Tinkerforge/distance-us-v2-bricklet-techniker/Dokumentation/Ausarbeitung Technikerprojekt/0_Titelseite.tex

\begin{center}
\begin{Huge}
\textcolor{blue}{\textbf{Entwicklung und testen eines Ultraschall-Entfernungsmessers als Vorbereitung eines Produktentwurfes}}
\end{Huge}
\rule{\textwidth}{.4pt}
\vspace{1.5cm}
% Weiter in großer Schrift

\huge{\textbf{Projektarbeit}}\\
\begin{Large}
erstellt an der\\
Fachschule für Technik des Carl-Severing-Berufskolleg\\
für Metall- und Elektrotechnik der Stadt Bielefeld\\
\\

Erstellt durch:\\
\vspace{12pt}
Eduard Meiser\\Omar Hachimi \\Stephan Dannat\\FET6A\\
\vspace{12pt}
in Zusammenarbeit mit der Fa. Tinkerforge\\
betreut durch\\
Herrn Simon\\
Bielefeld, \today
\end{Large}
\end{center}
