Tinkerforge/distance-us-v2-bricklet-techniker/Dokumentation/Anhänge/C4016L8A40_Ultraschallsensor.pdf

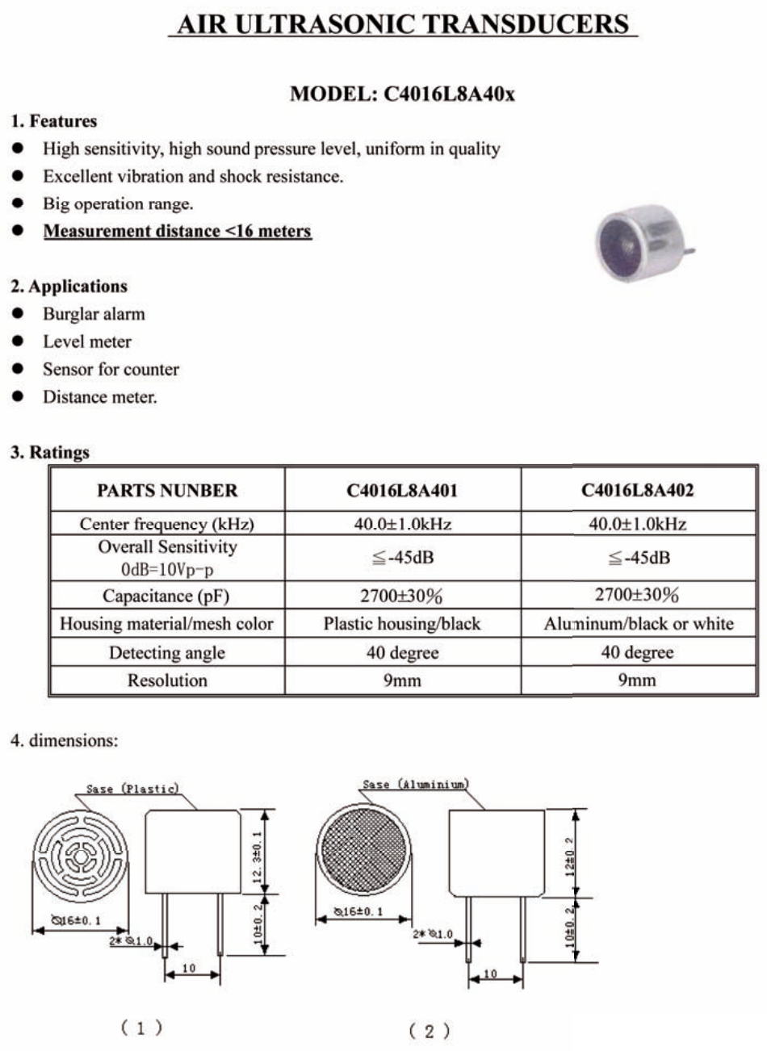
[picture p30: page 1]
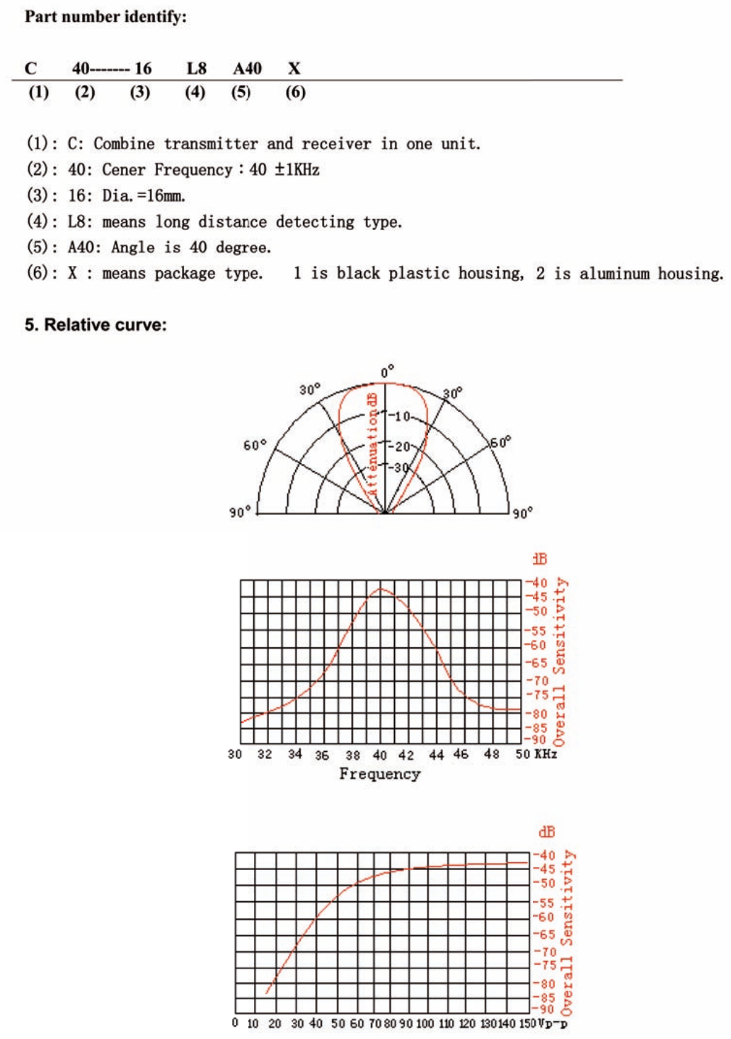
[picture p31: page 2]
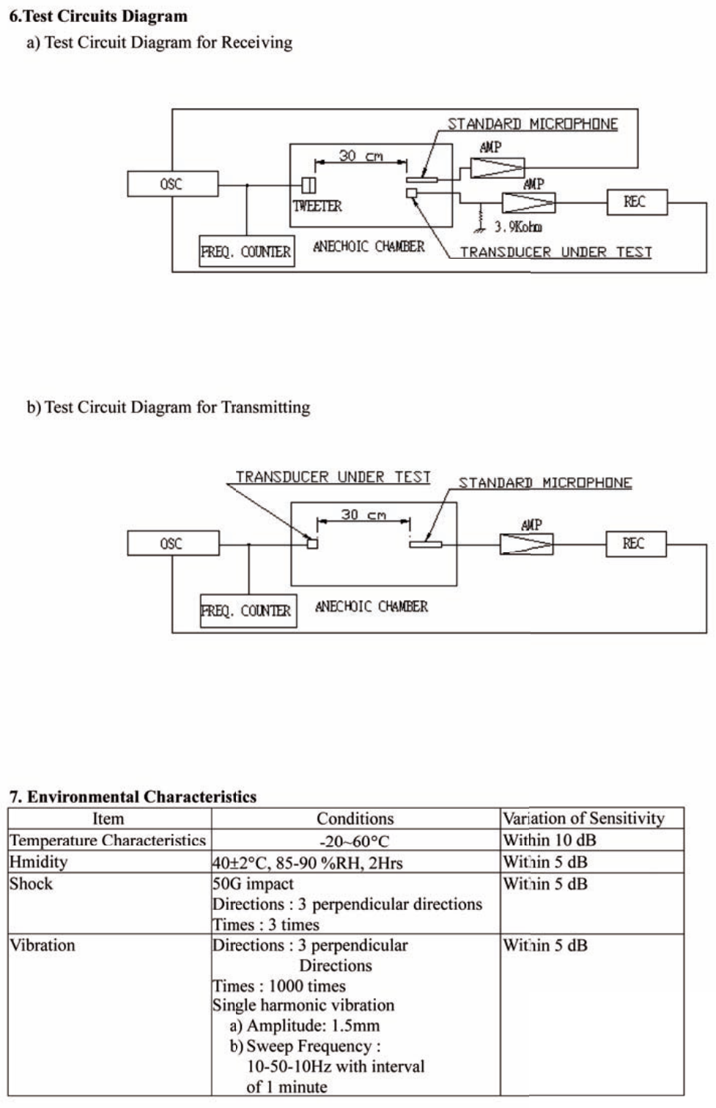
[picture p32: page 3]
