Tinkerforge/distance-us-v2-bricklet-techniker/Dokumentation/Ausarbeitung Technikerprojekt/Abbildungen/A5950/H_Brücke.jpg

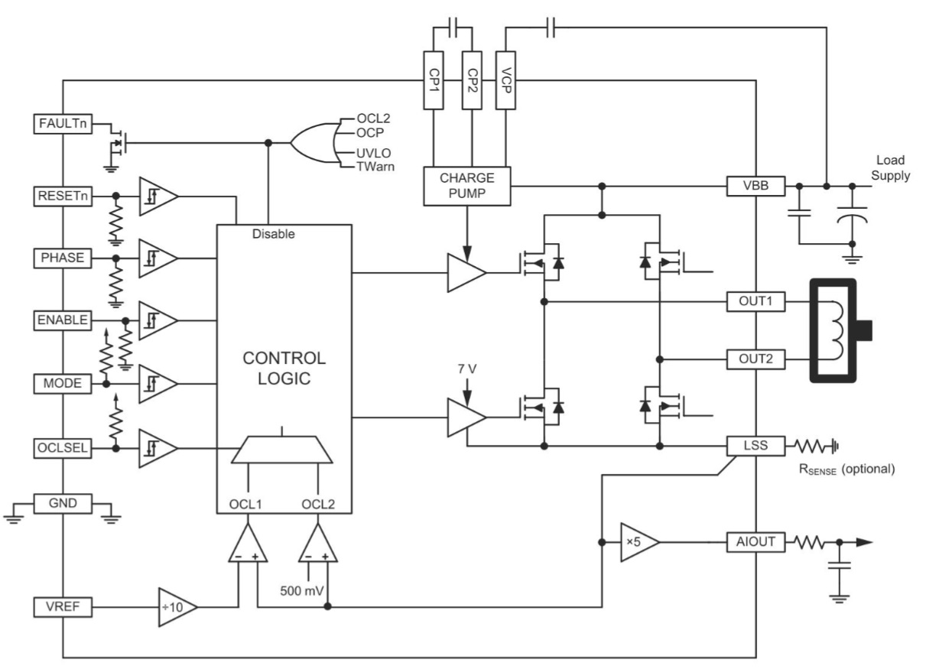
Dokumentation/Ausarbeitung Technikerprojekt/Abbildungen/A5950/H_Brücke.jpg
