Tinkerforge/distance-us-v2-bricklet-techniker/Dokumentation/Ausarbeitung Technikerprojekt/Abbildungen/Empfaenger.png

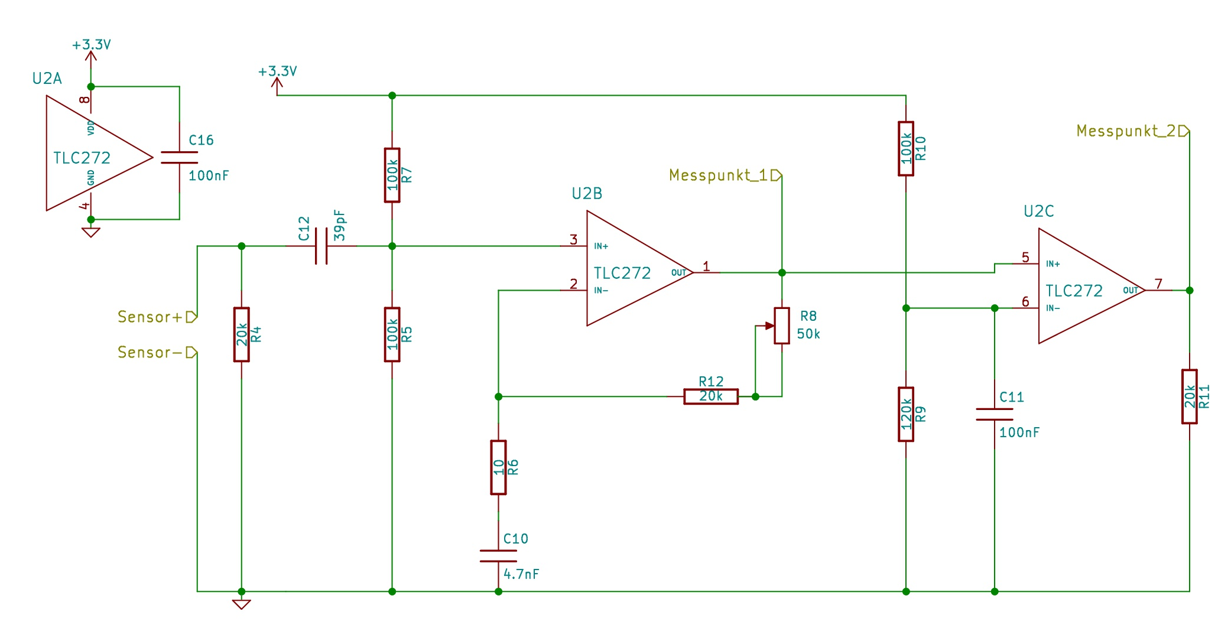
Dokumentation/Ausarbeitung Technikerprojekt/Abbildungen/Empfaenger.png
