Tinkerforge/distance-us-v2-bricklet-techniker/Dokumentation/Ausarbeitung Technikerprojekt/Abbildungen/h-side.jpg

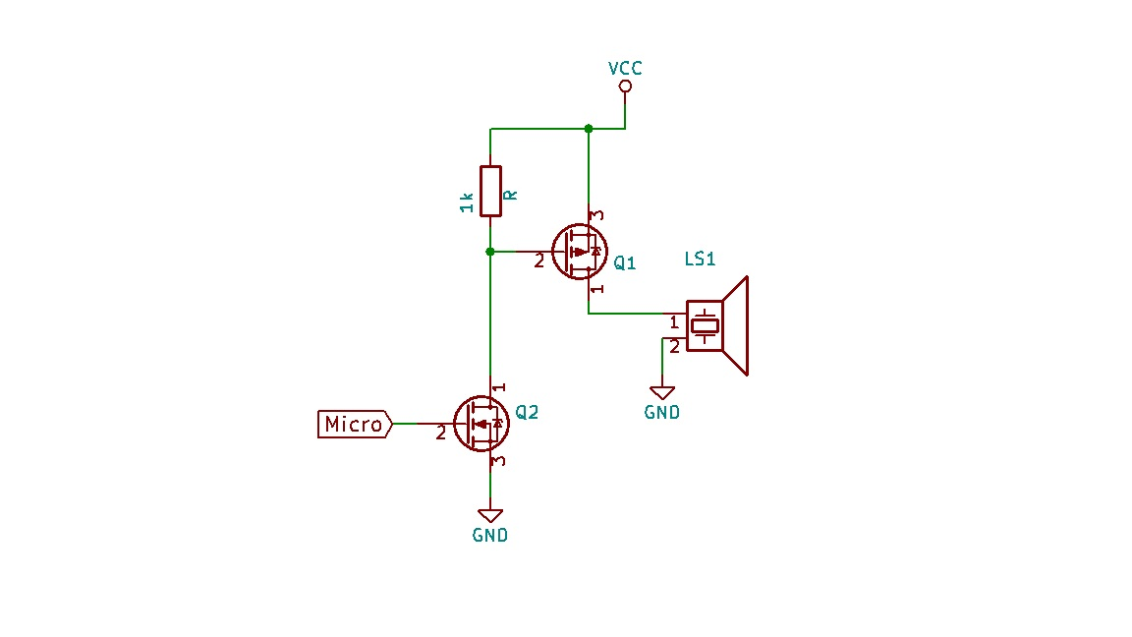
Dokumentation/Ausarbeitung Technikerprojekt/Abbildungen/h-side.jpg
