Tinkerforge/distance-us-v2-bricklet-techniker/Dokumentation/Ausarbeitung Technikerprojekt/Abbildungen/h-side.png

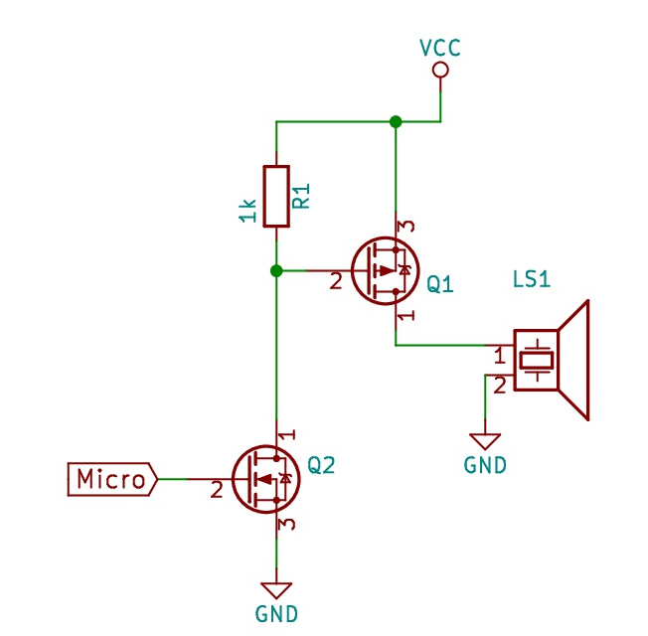
Dokumentation/Ausarbeitung Technikerprojekt/Abbildungen/h-side.png
