Tinkerforge/distance-us-v2-bricklet-techniker/Dokumentation/Ausarbeitung Technikerprojekt/Abbildungen/halbbrucke.png

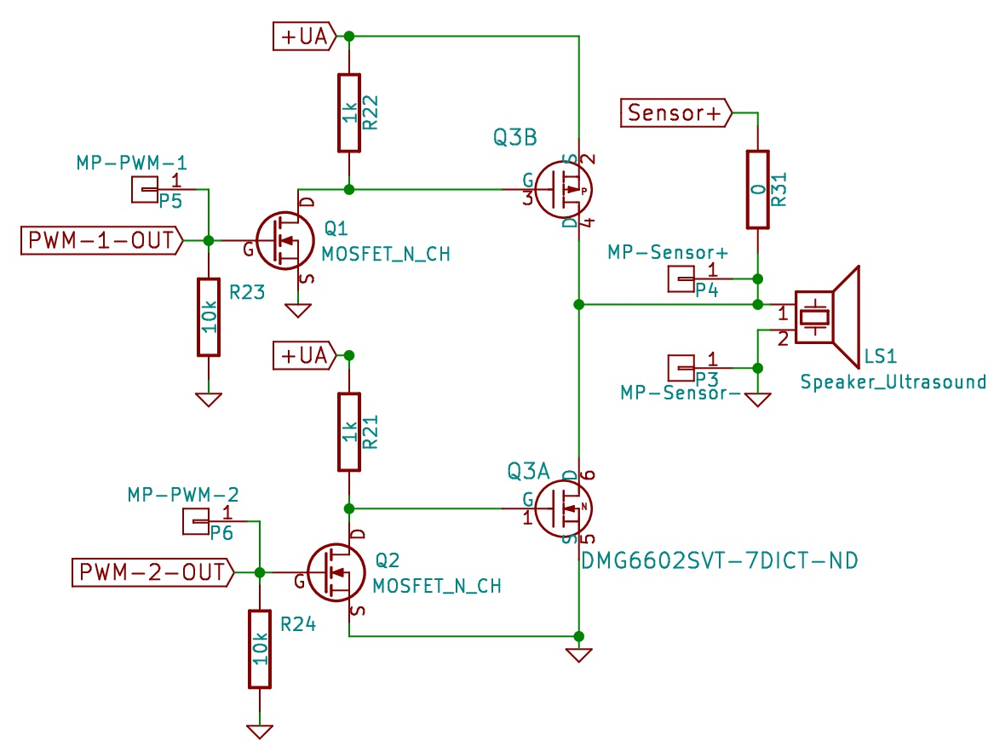
Dokumentation/Ausarbeitung Technikerprojekt/Abbildungen/halbbrucke.png
