Tinkerforge/distance-us-v2-bricklet-techniker/Dokumentation/Ausarbeitung Technikerprojekt/Abbildungen/MessungenP1/EKULIT1,5m.PNG

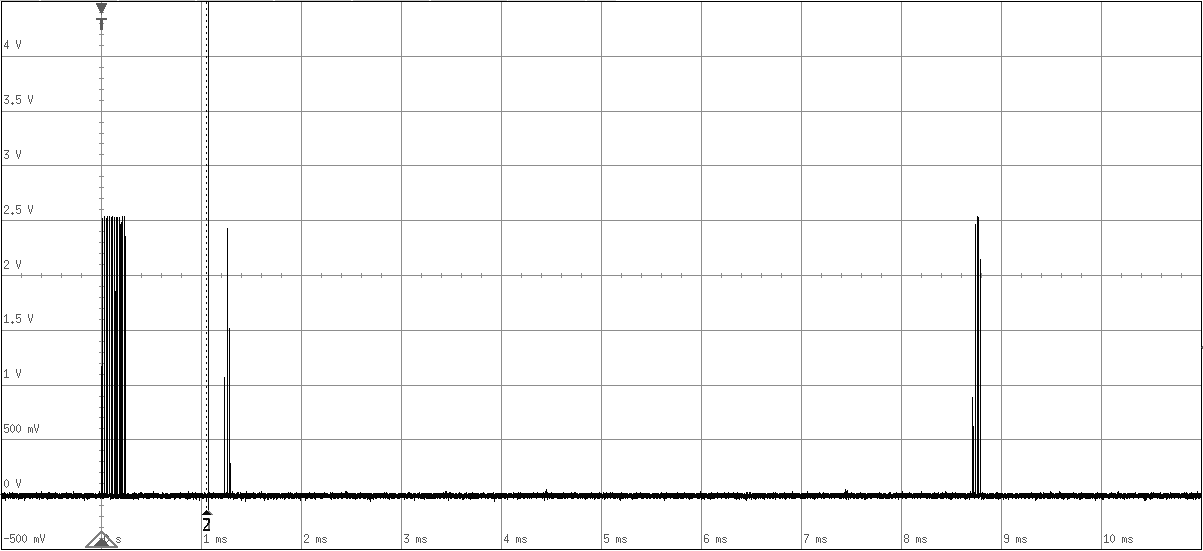
Dokumentation/Ausarbeitung Technikerprojekt/Abbildungen/MessungenP1/EKULIT1,5m.PNG
