Tinkerforge/distance-us-v2-bricklet-techniker/Dokumentation/Ausarbeitung Technikerprojekt/Abbildungen/MessungenP1/EKULIT2,3m.PNG

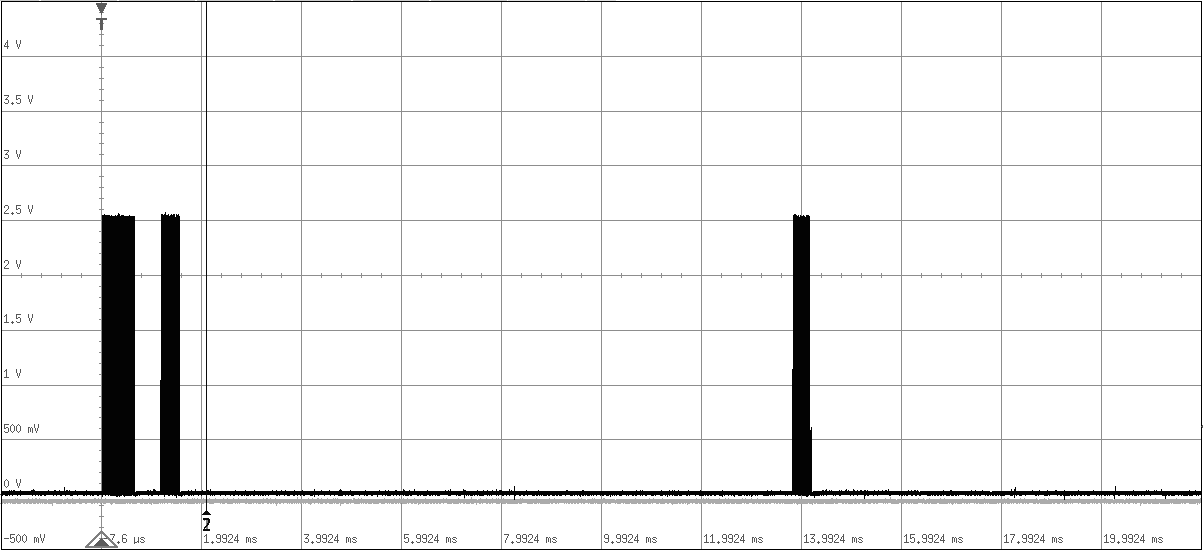
Dokumentation/Ausarbeitung Technikerprojekt/Abbildungen/MessungenP1/EKULIT2,3m.PNG
