Tinkerforge/distance-us-v2-bricklet-techniker/Dokumentation/Ausarbeitung Technikerprojekt/Abbildungen/MessungenP1/MURATAr1,5m.PNG

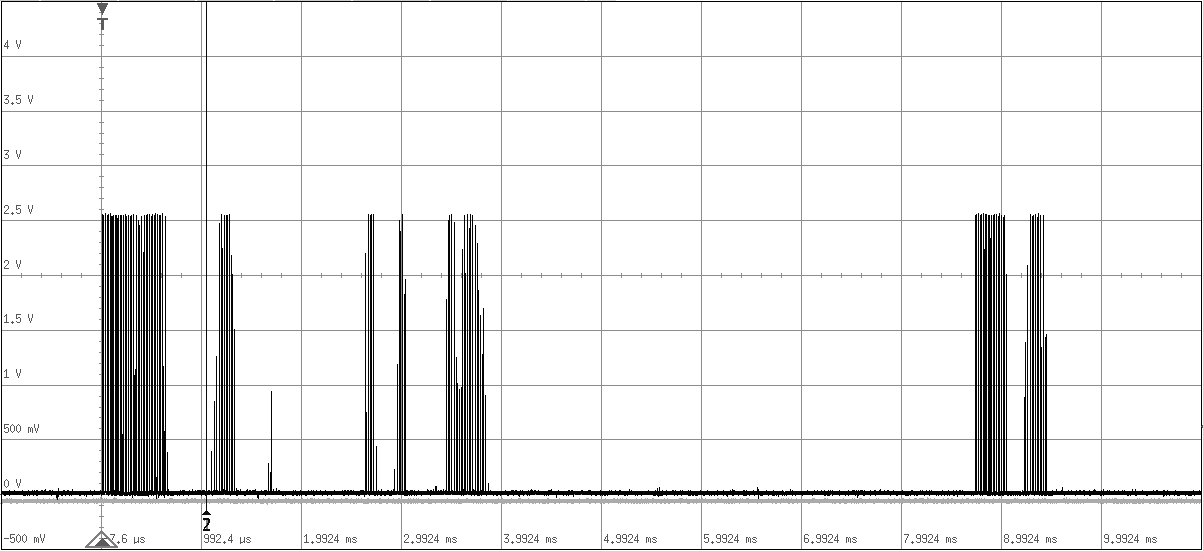
Dokumentation/Ausarbeitung Technikerprojekt/Abbildungen/MessungenP1/MURATAr1,5m.PNG
