Tinkerforge/distance-us-v2-bricklet-techniker/Dokumentation/Ausarbeitung Technikerprojekt/Abbildungen/MessungenP1/MURATAr20cm.PNG

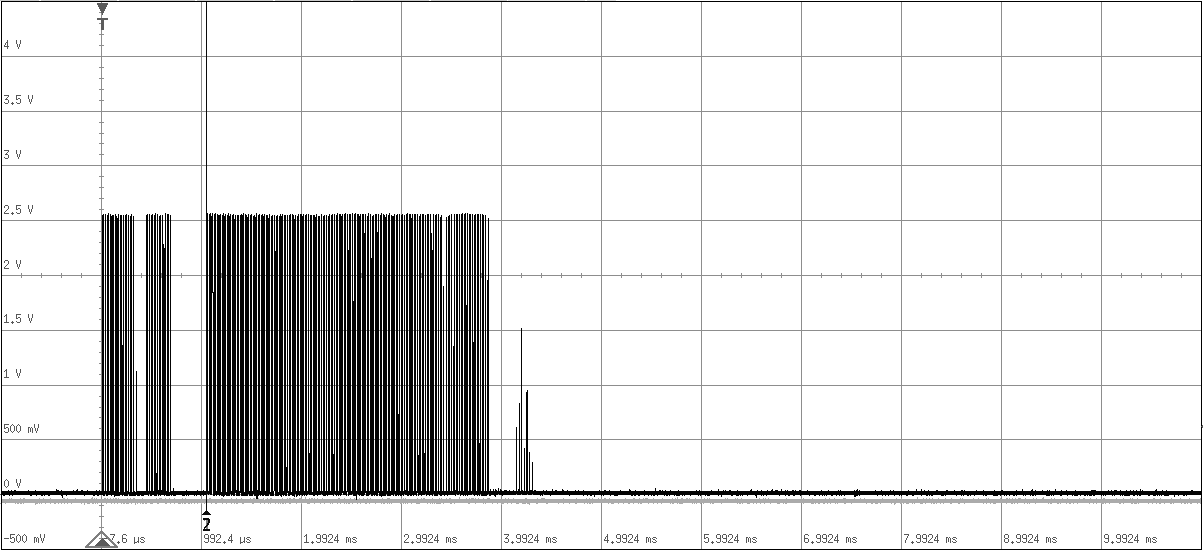
Dokumentation/Ausarbeitung Technikerprojekt/Abbildungen/MessungenP1/MURATAr20cm.PNG
