Tinkerforge/distance-us-v2-bricklet-techniker/Dokumentation/Ausarbeitung Technikerprojekt/Abbildungen/MessungenP1/MURATAs20cm.PNG

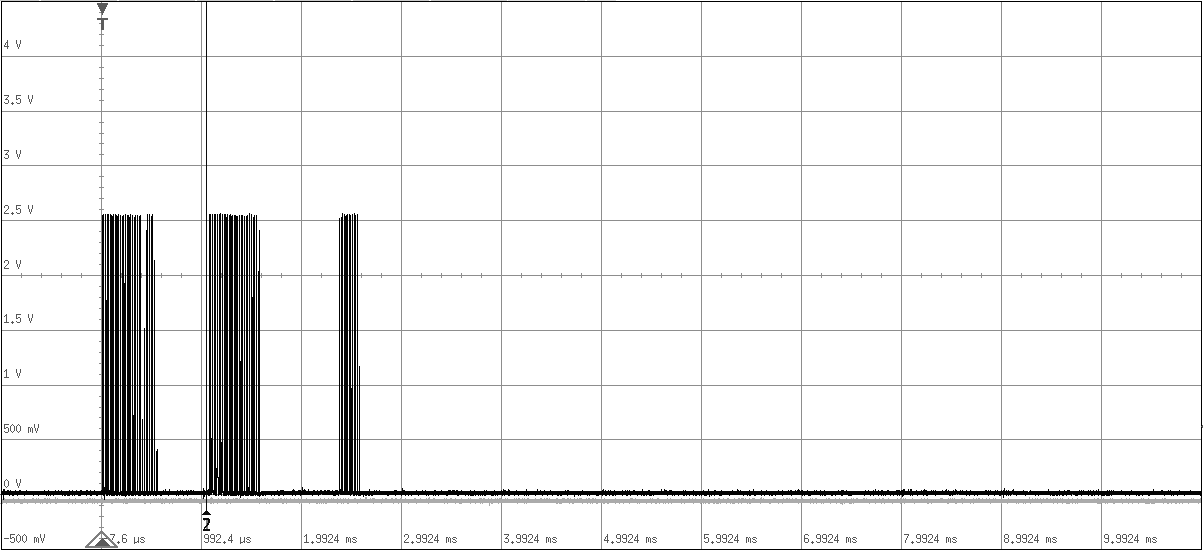
Dokumentation/Ausarbeitung Technikerprojekt/Abbildungen/MessungenP1/MURATAs20cm.PNG
