Tinkerforge/distance-us-v2-bricklet-techniker/Dokumentation/Ausarbeitung Technikerprojekt/Abbildungen/MessungenP1/Nachschwingen am Verstarker mit LS.PNG

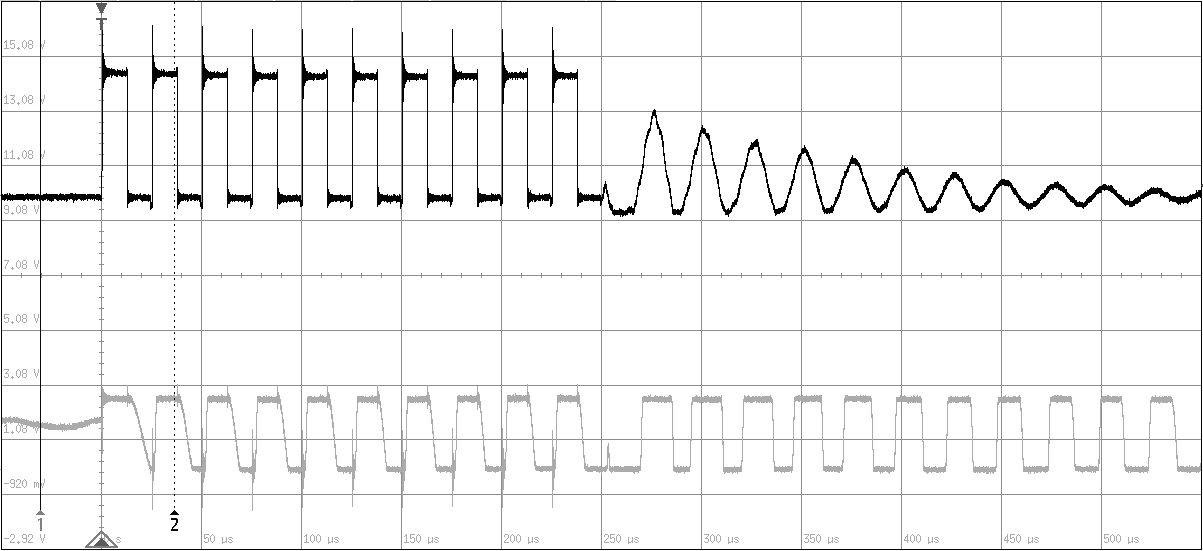
Dokumentation/Ausarbeitung Technikerprojekt/Abbildungen/MessungenP1/Nachschwingen am Verstarker mit LS.PNG
