Tinkerforge/distance-us-v2-bricklet-techniker/Dokumentation/Ausarbeitung Technikerprojekt/Abbildungen/MessungenP1/PWM-ausgabe-mit-Hi-Side.PNG

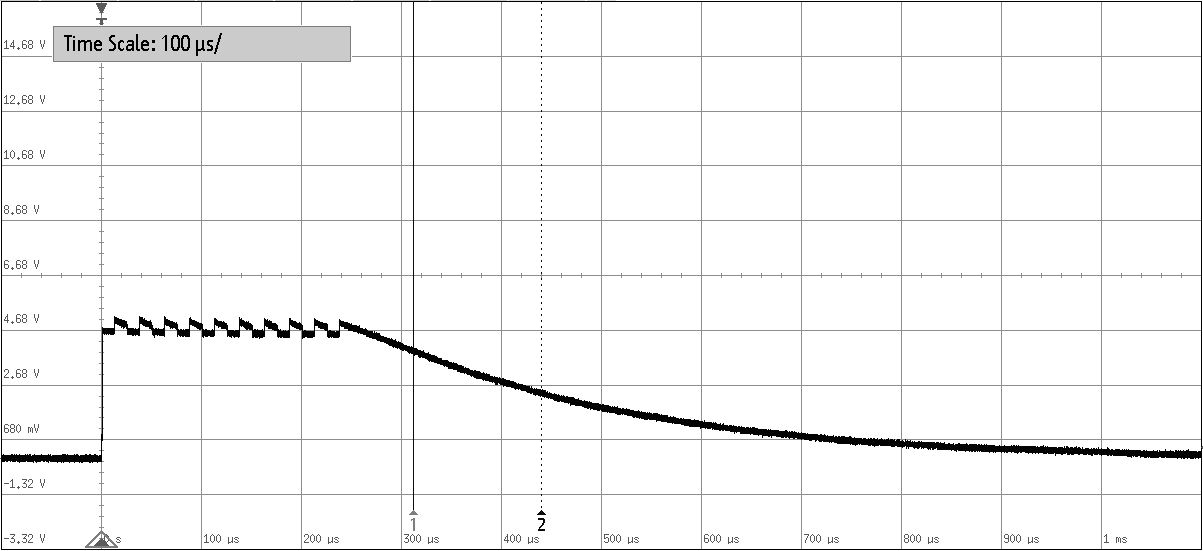
Dokumentation/Ausarbeitung Technikerprojekt/Abbildungen/MessungenP1/PWM-ausgabe-mit-Hi-Side.PNG
