Tinkerforge/distance-us-v2-bricklet-techniker/Dokumentation/Ausarbeitung Technikerprojekt/Abbildungen/MessungenP1/PWM-Nach-der-Halbbrucke-mit-LS.PNG

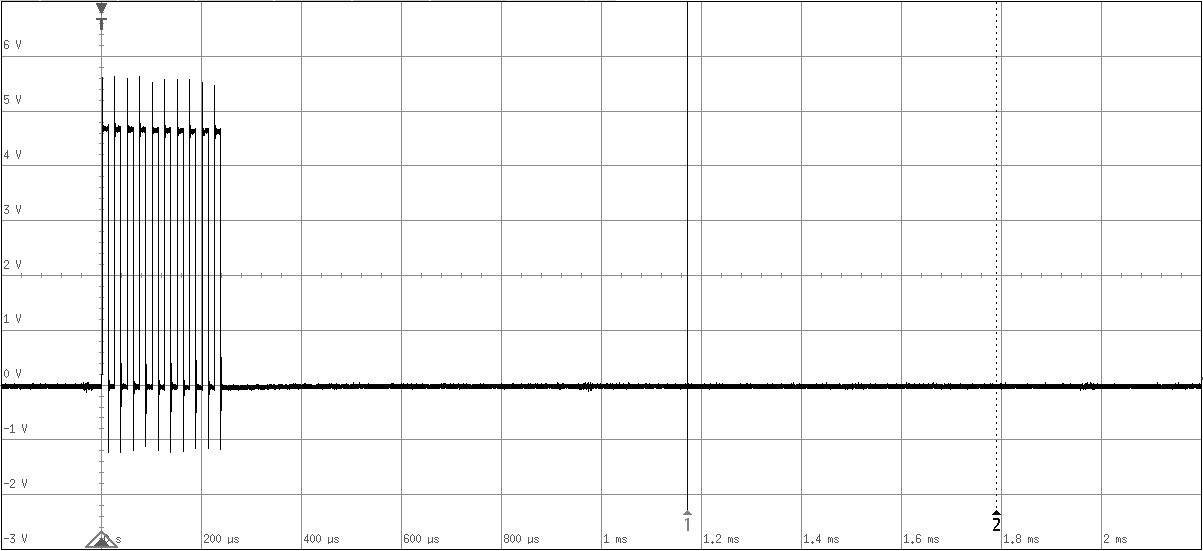
Dokumentation/Ausarbeitung Technikerprojekt/Abbildungen/MessungenP1/PWM-Nach-der-Halbbrucke-mit-LS.PNG
