Tinkerforge/distance-us-v2-bricklet-techniker/Dokumentation/Ausarbeitung Technikerprojekt/Abbildungen/MessungenP1/PWM-Signal-invertiert.PNG

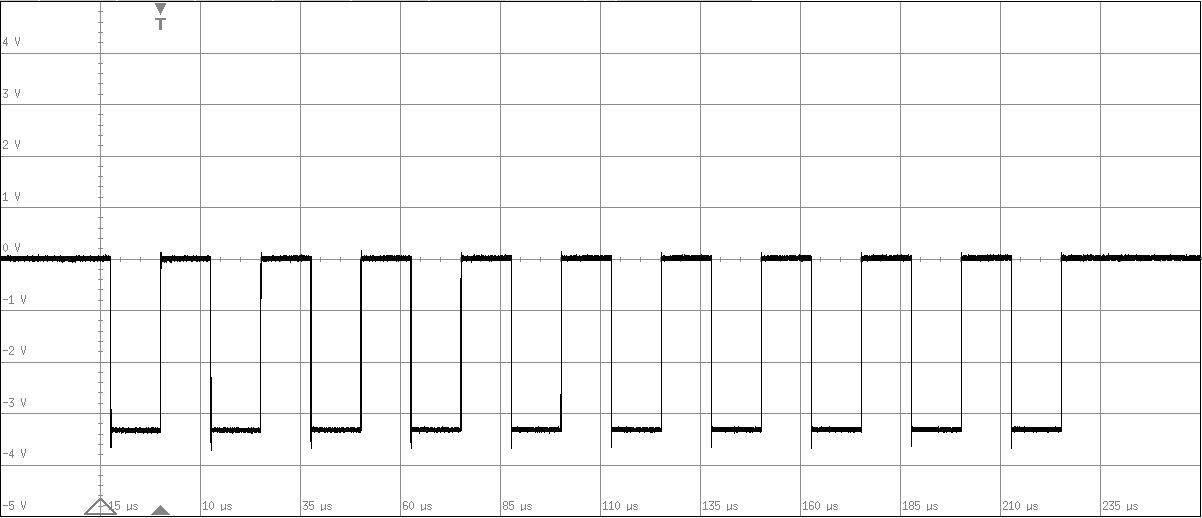
Dokumentation/Ausarbeitung Technikerprojekt/Abbildungen/MessungenP1/PWM-Signal-invertiert.PNG
