Tinkerforge/distance-us-v2-bricklet-techniker/Dokumentation/Ausarbeitung Technikerprojekt/Abbildungen/MessungenP1/PWM-von-der-CPU.PNG

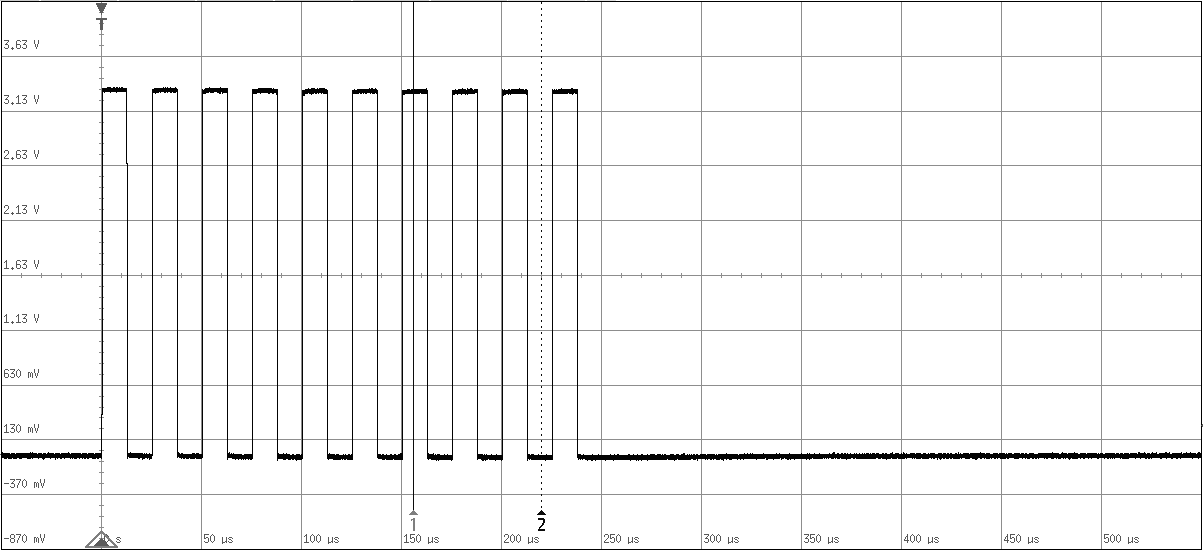
Dokumentation/Ausarbeitung Technikerprojekt/Abbildungen/MessungenP1/PWM-von-der-CPU.PNG
