Tinkerforge/distance-us-v2-bricklet-techniker/Dokumentation/Ausarbeitung Technikerprojekt/Abbildungen/MessungenP1/Signal am Lautsprecher mit Empfang.PNG

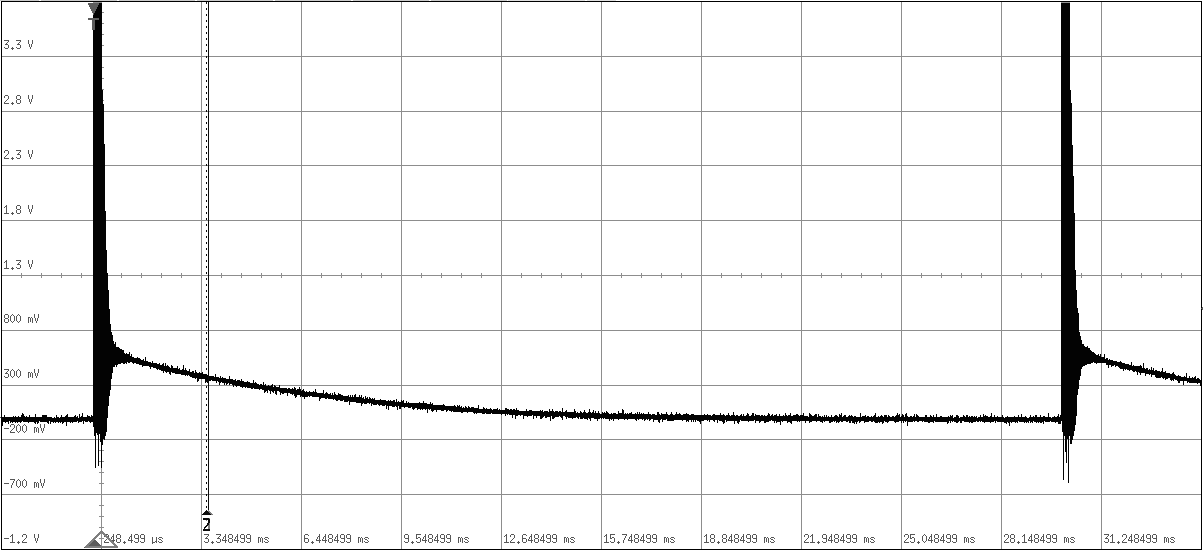
Dokumentation/Ausarbeitung Technikerprojekt/Abbildungen/MessungenP1/Signal am Lautsprecher mit Empfang.PNG
