Tinkerforge/distance-us-v2-bricklet-techniker/Dokumentation/Ausarbeitung Technikerprojekt/Abbildungen/MessungenP1/Signal-Empfang.PNG

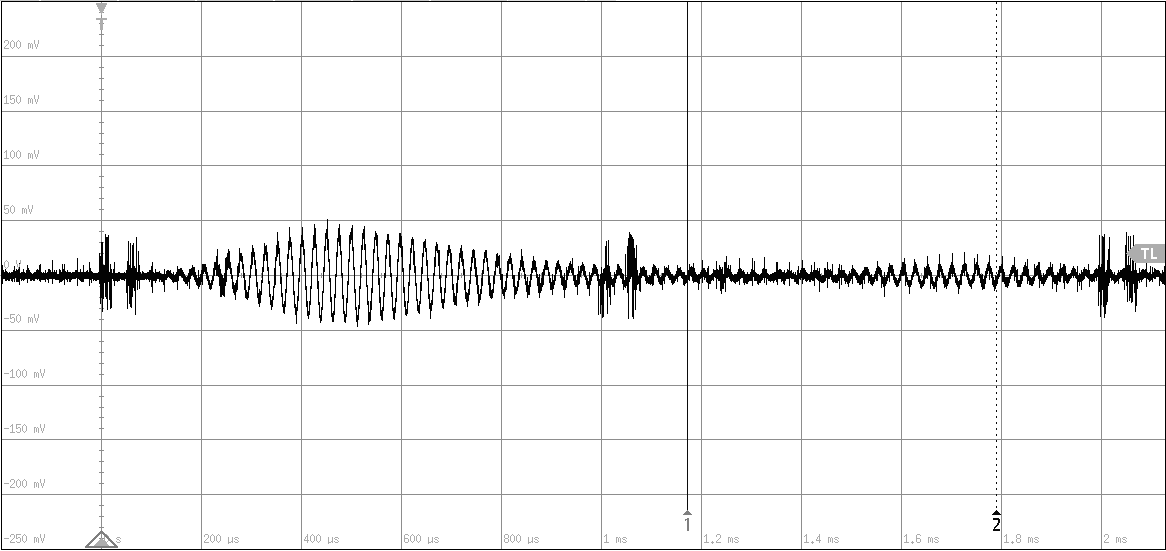
Dokumentation/Ausarbeitung Technikerprojekt/Abbildungen/MessungenP1/Signal-Empfang.PNG
