Tinkerforge/distance-us-v2-bricklet-techniker/Dokumentation/Ausarbeitung Technikerprojekt/Abbildungen/MessungenP1/Signal-nach-der-Filterung.PNG

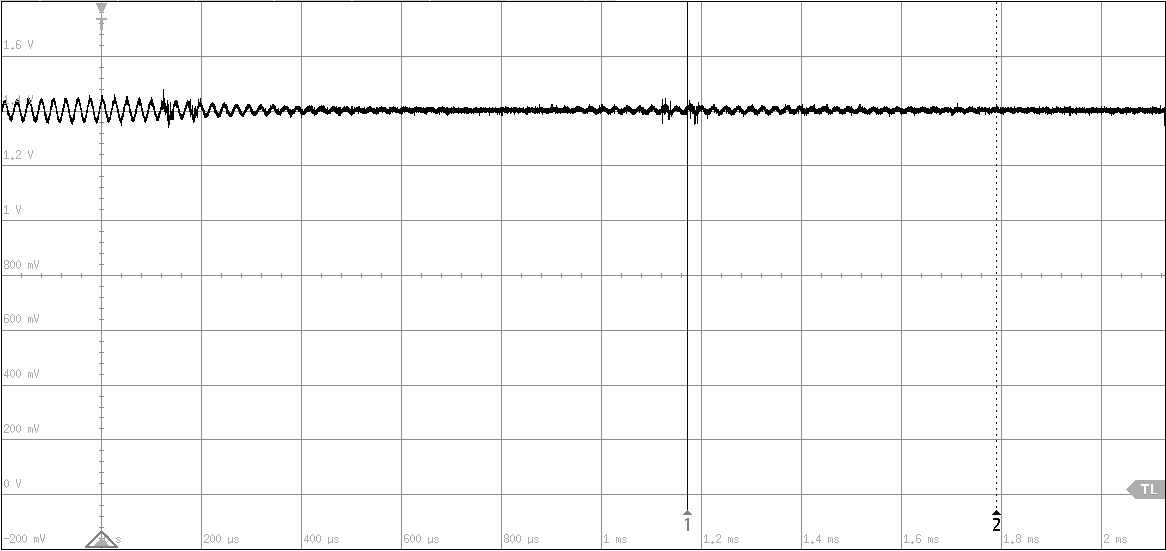
Dokumentation/Ausarbeitung Technikerprojekt/Abbildungen/MessungenP1/Signal-nach-der-Filterung.PNG
