Tinkerforge/distance-us-v2-bricklet-techniker/Dokumentation/Ausarbeitung Technikerprojekt/Abbildungen/MessungenP2/4,6V/EKULIT1,5m.PNG

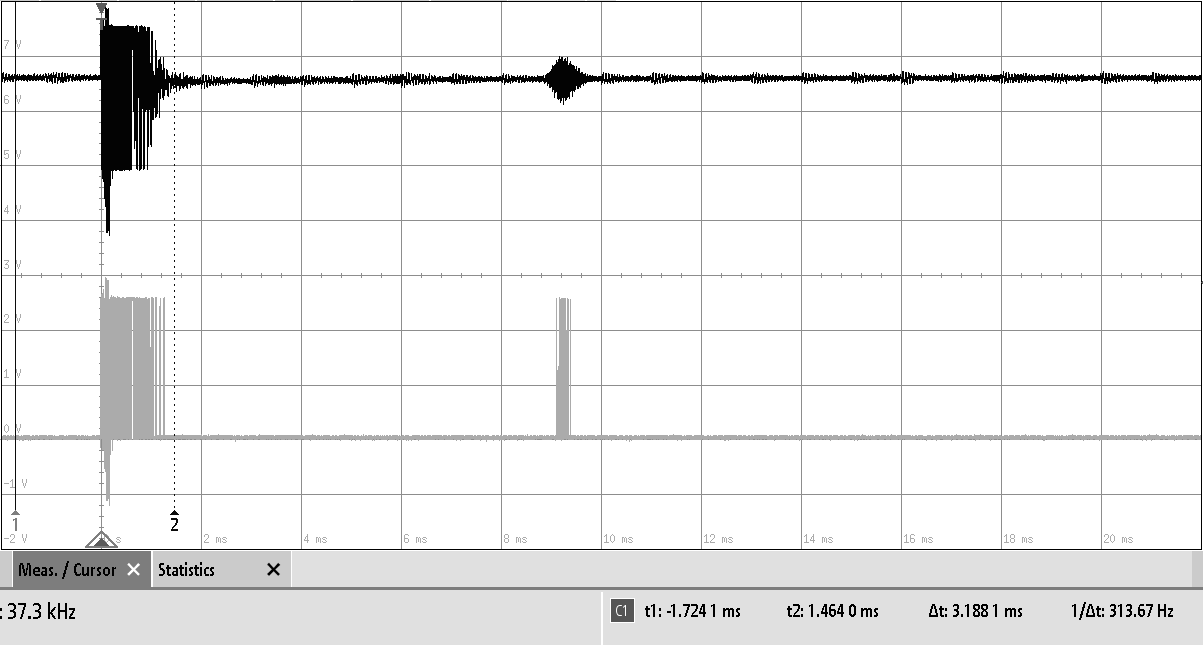
Dokumentation/Ausarbeitung Technikerprojekt/Abbildungen/MessungenP2/4,6V/EKULIT1,5m.PNG
