Tinkerforge/distance-us-v2-bricklet-techniker/Dokumentation/Ausarbeitung Technikerprojekt/Abbildungen/MessungenP2/5V/1,5m.PNG

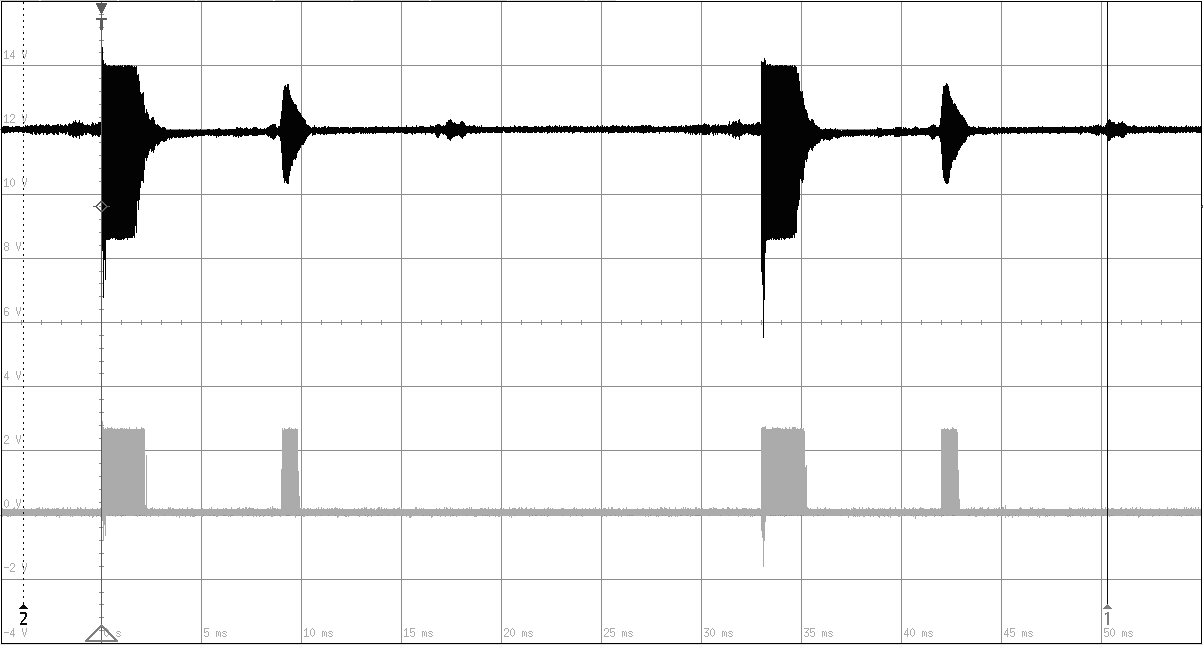
Dokumentation/Ausarbeitung Technikerprojekt/Abbildungen/MessungenP2/5V/1,5m.PNG
