Tinkerforge/distance-us-v2-bricklet-techniker/Dokumentation/Ausarbeitung Technikerprojekt/Abbildungen/MessungenP2/5V/1m.PNG

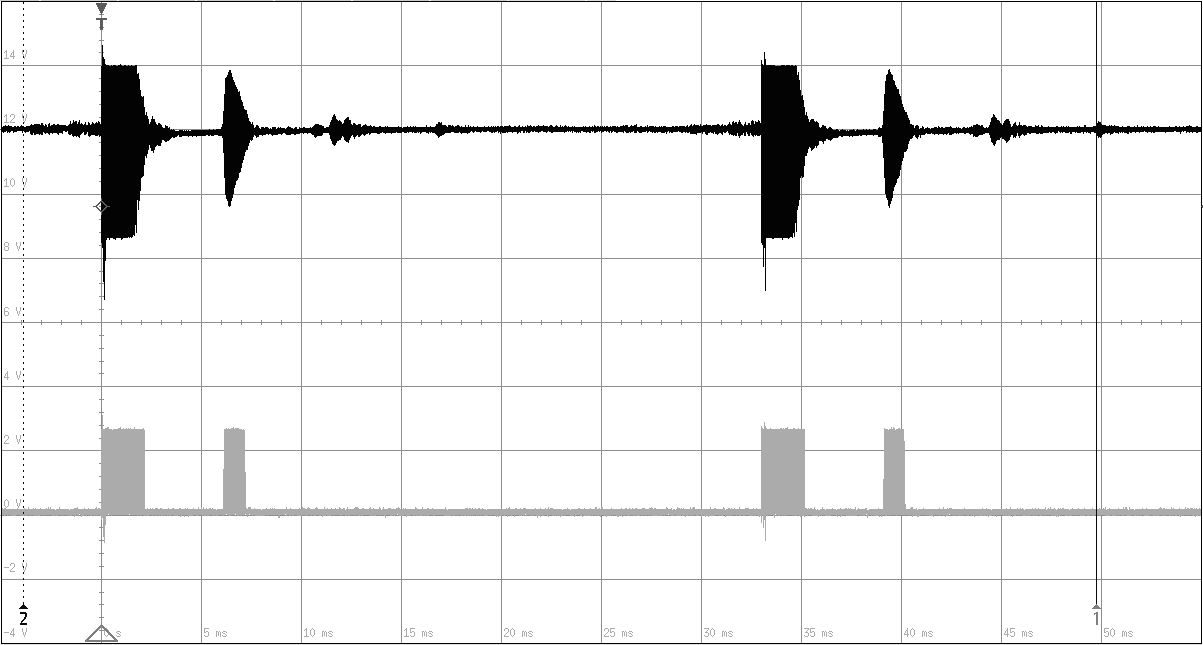
Dokumentation/Ausarbeitung Technikerprojekt/Abbildungen/MessungenP2/5V/1m.PNG
