Tinkerforge/distance-us-v2-bricklet-techniker/Dokumentation/Ausarbeitung Technikerprojekt/Abbildungen/MessungenP2/EKULIT1m10V.PNG

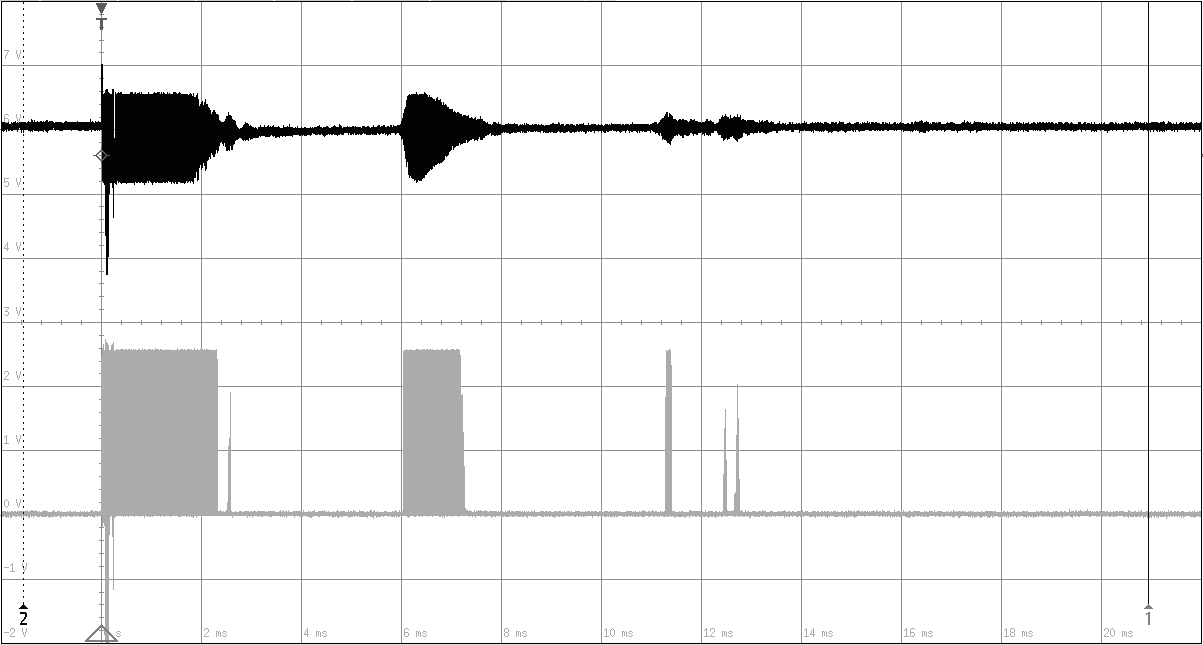
Dokumentation/Ausarbeitung Technikerprojekt/Abbildungen/MessungenP2/EKULIT1m10V.PNG
