Tinkerforge/distance-us-v2-bricklet-techniker/Dokumentation/Ausarbeitung Technikerprojekt/Abbildungen/MessungenP2/Messung_nach_der_Filterung_40pF.PNG

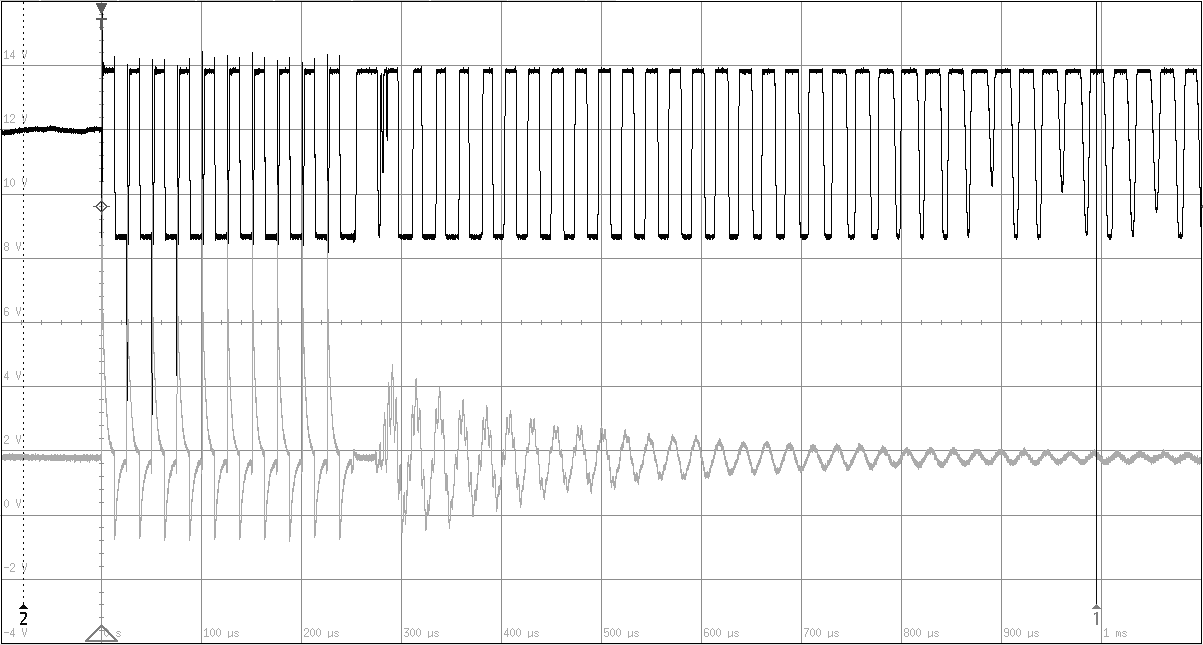
Dokumentation/Ausarbeitung Technikerprojekt/Abbildungen/MessungenP2/Messung_nach_der_Filterung_40pF.PNG
