Tinkerforge/distance-us-v2-bricklet-techniker/Dokumentation/Ausarbeitung Technikerprojekt/Abbildungen/MessungenP2/Messung_nach_der_Filterung_100nF_ohne_R1.PNG

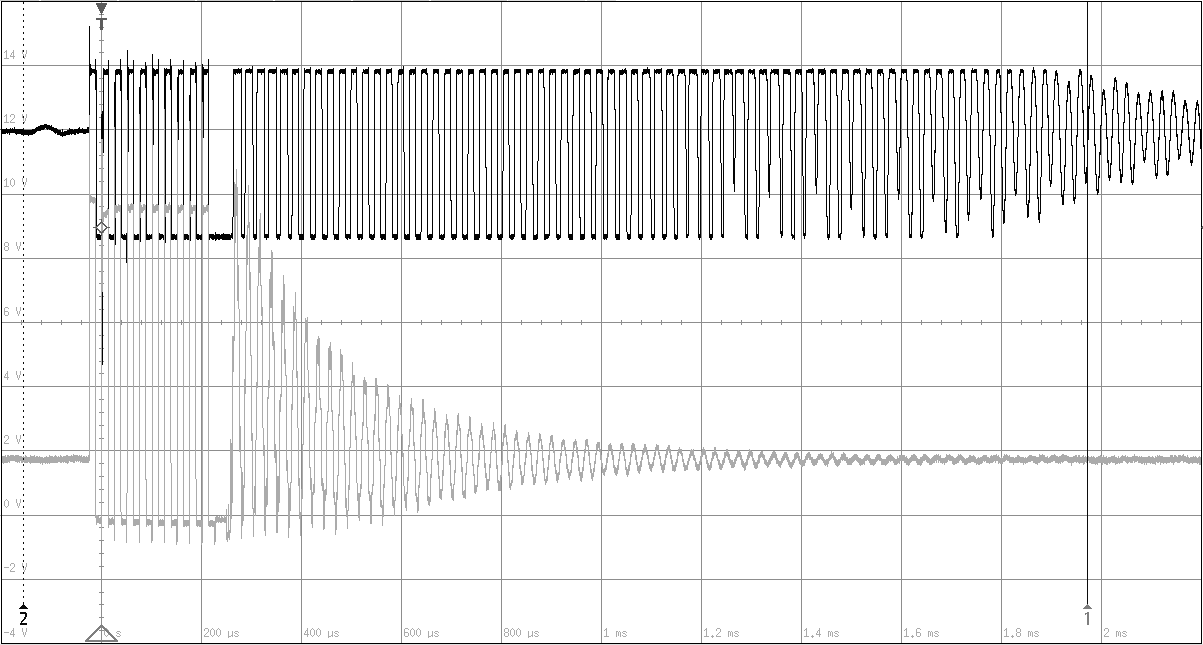
Dokumentation/Ausarbeitung Technikerprojekt/Abbildungen/MessungenP2/Messung_nach_der_Filterung_100nF_ohne_R1.PNG
