Tinkerforge/distance-us-v2-bricklet-techniker/Strkutogramm/a16pt.png

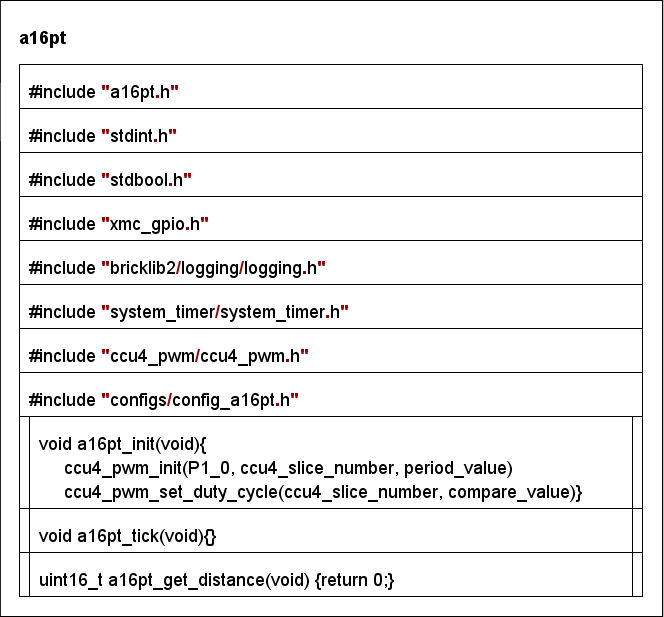
Strkutogramm/a16pt.png
