Tinkerforge/distance-us-v2-bricklet-techniker/Strkutogramm/Communication.png

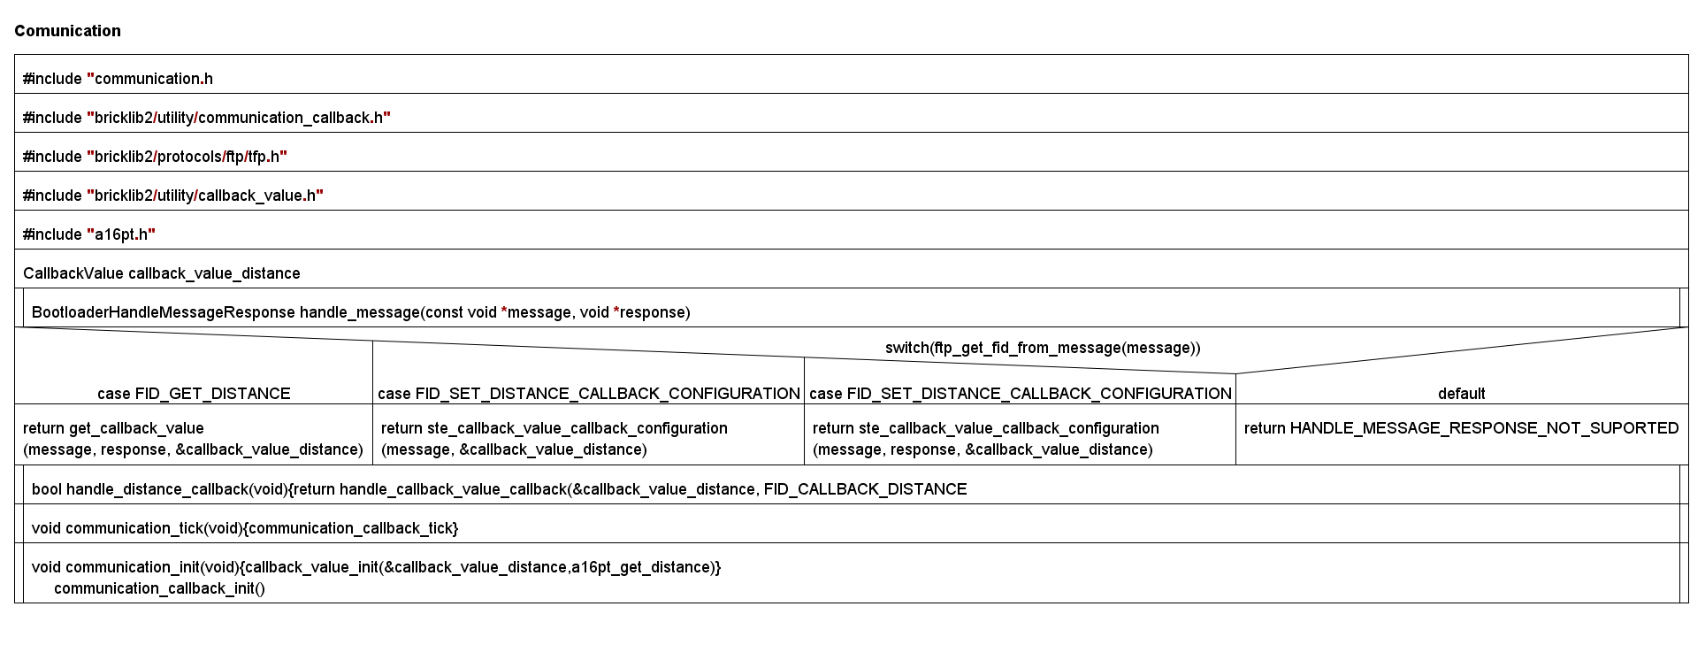
Strkutogramm/Communication.png
