Tinkerforge/distance-us-v2-bricklet-techniker/Strkutogramm/Main.png

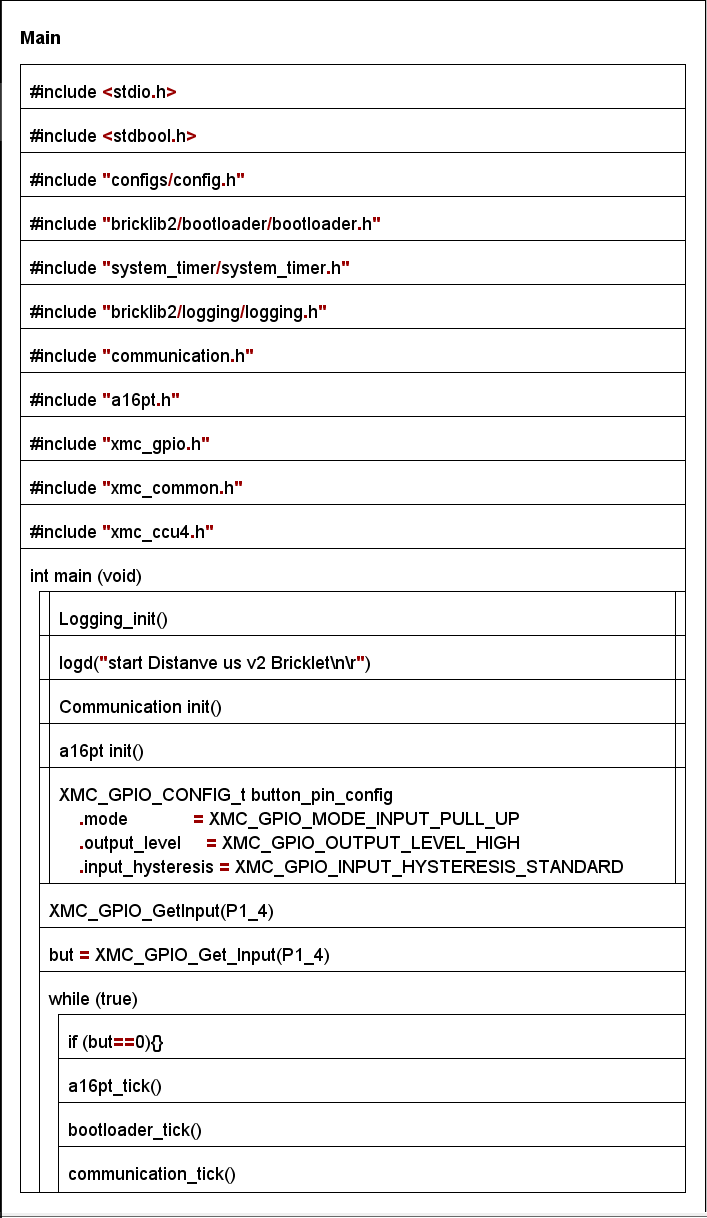
Strkutogramm/Main.png
