Tinkerforge/distance-us-v2-bricklet-techniker/software/src/config_pin/config_pin.c

#include "config_pin.h"


void pin_in_pullup_init(XMC_GPIO_PORT_t *const port, const uint8_t pin)
{
  const	XMC_GPIO_CONFIG_t pin_in_config = {
  			.mode             = XMC_GPIO_MODE_INPUT_PULL_UP,
  			.output_level     = XMC_GPIO_OUTPUT_LEVEL_HIGH,
  			.input_hysteresis	= XMC_GPIO_INPUT_HYSTERESIS_STANDARD
  		};

  XMC_GPIO_Init(port, pin, &pin_in_config);

}

void pin_out_init(XMC_GPIO_PORT_t *const port, const uint8_t pin)
{
const XMC_GPIO_CONFIG_t pin_out_config	= {
		.mode                = XMC_GPIO_MODE_OUTPUT_PUSH_PULL,
		.output_level        = XMC_GPIO_OUTPUT_LEVEL_LOW,
	};

  XMC_GPIO_Init(port, pin, &pin_out_config);

}
